aitesam961/Cattle-Health-Monitoring-WSN/Documentation/Video/CDC/20230429_175326.jpg

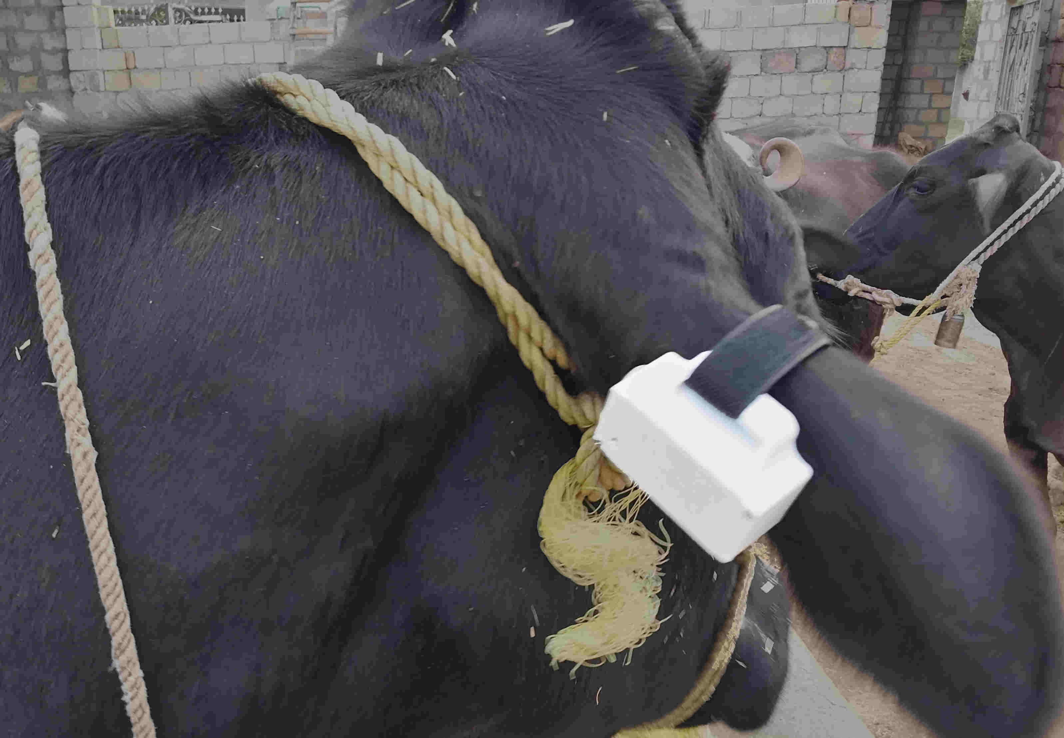
Documentation/Video/CDC/20230429_175326.jpg
