aitesam961/Cattle-Health-Monitoring-WSN/Documentation/Video/CDC/20230429_175645.jpg

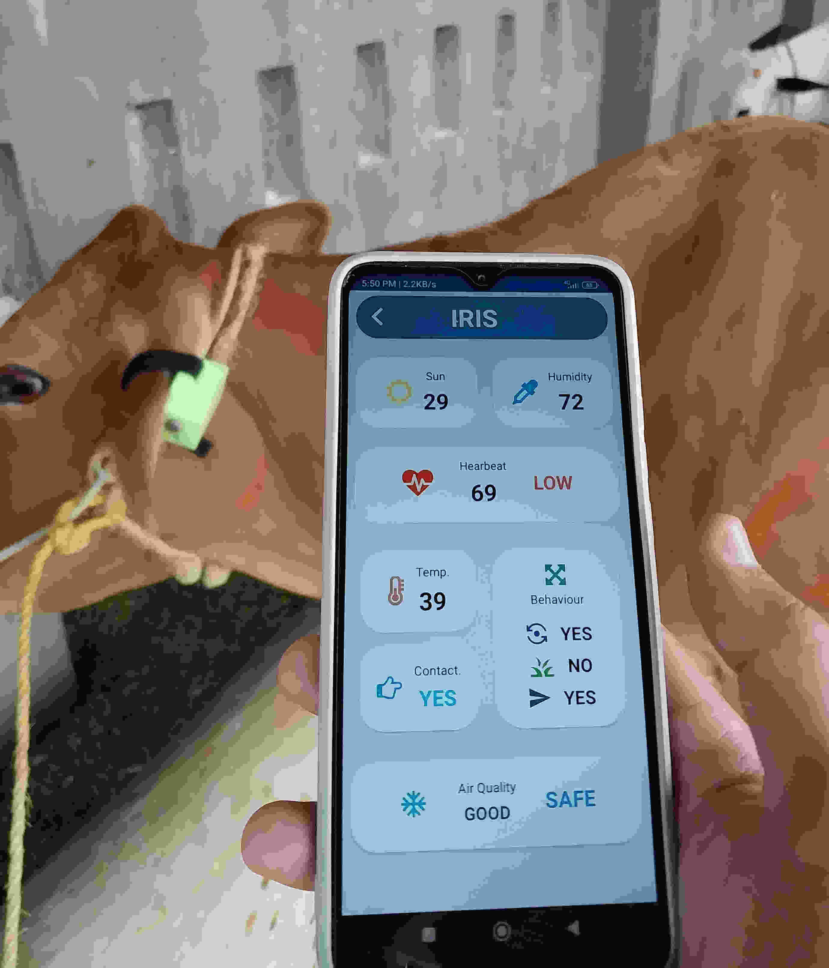
Documentation/Video/CDC/20230429_175645.jpg
