aitesam961/Cattle-Health-Monitoring-WSN/Documentation/Video/CDC/cows-7880154_1920_1_5.jpg

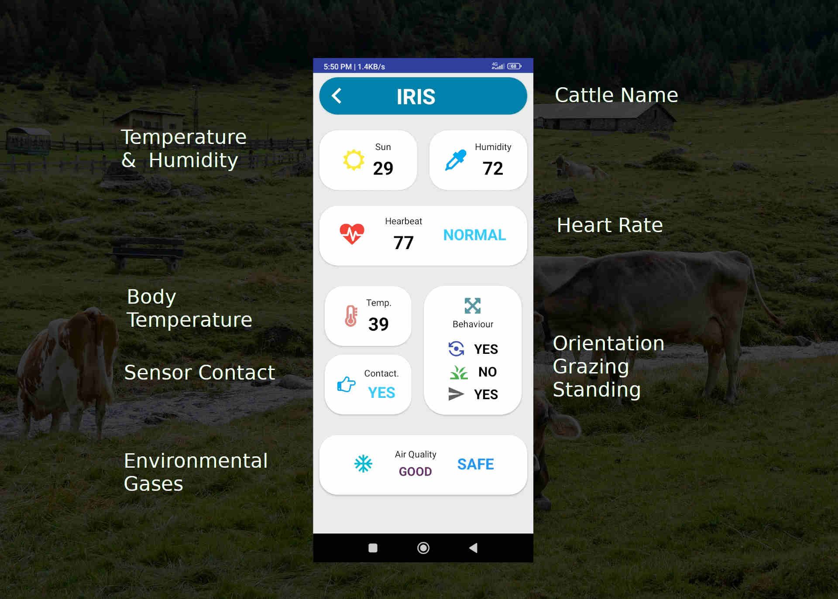
Documentation/Video/CDC/cows-7880154_1920_1_5.jpg
