aitesam961/Cattle-Health-Monitoring-WSN/Documentation/Video/CDC/IMG_20230511_132144.jpg

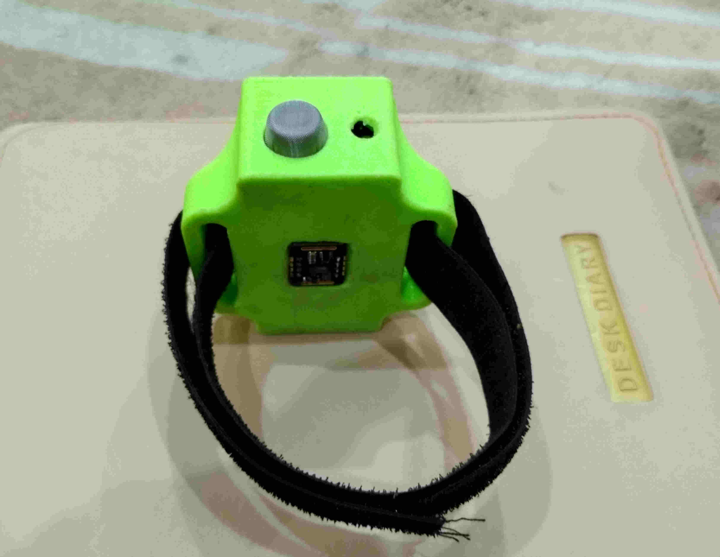
Documentation/Video/CDC/IMG_20230511_132144.jpg
