aitesam961/Cattle-Health-Monitoring-WSN/Documentation/Video/Video Workdir/cows-7990273_1920.jpg

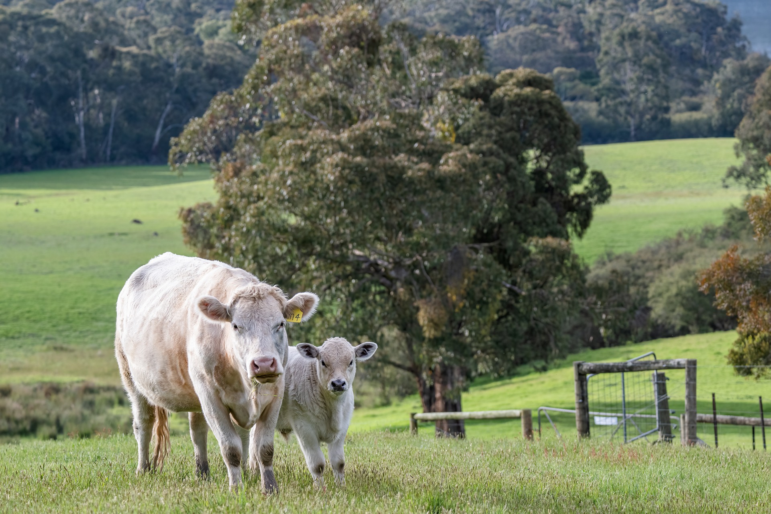
Documentation/Video/Video Workdir/cows-7990273_1920.jpg
