aitesam961/Cattle-Health-Monitoring-WSN/Documentation/Video/Video Workdir/DataAnalysis.jpg

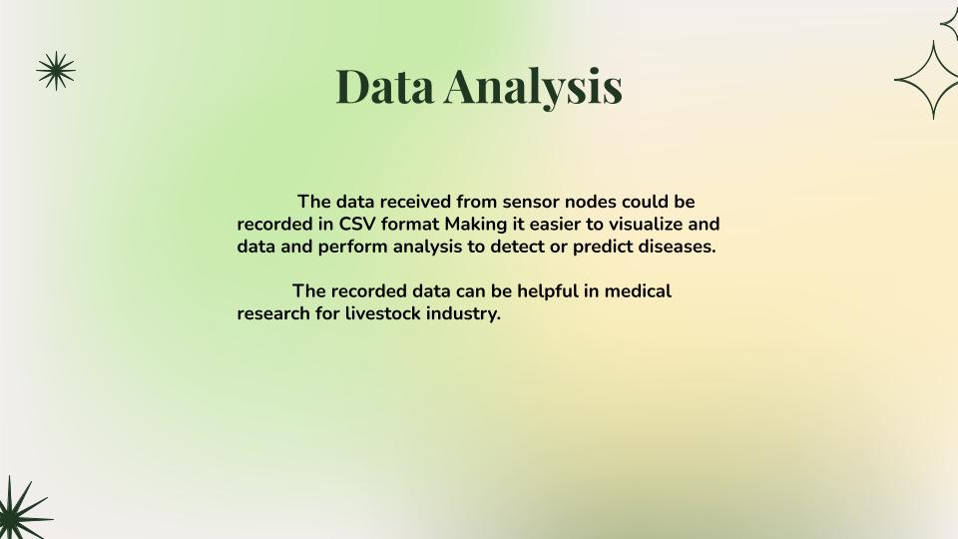
Documentation/Video/Video Workdir/DataAnalysis.jpg
