aitesam961/Cattle-Health-Monitoring-WSN/Documentation/Video/Video Workdir/farming-7290365_1920.jpg

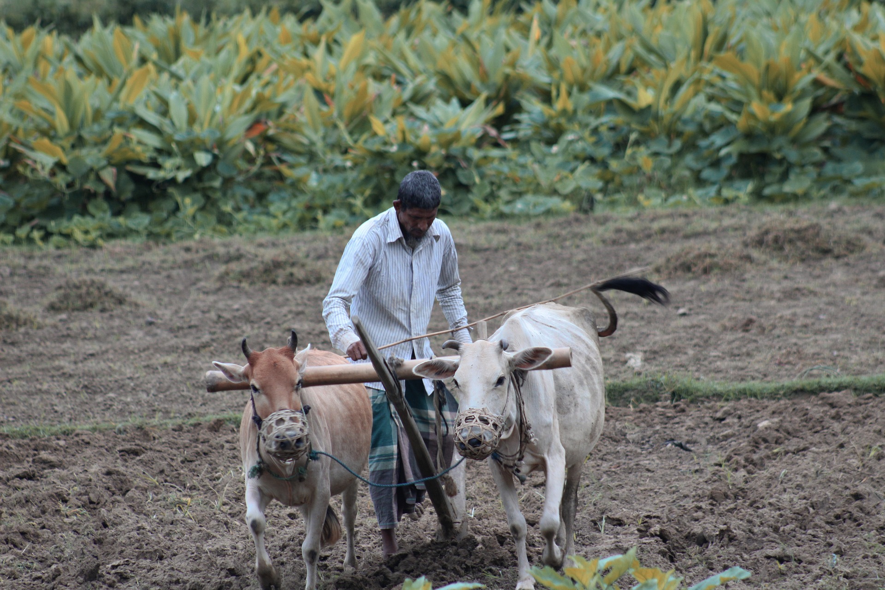
Documentation/Video/Video Workdir/farming-7290365_1920.jpg
