aitesam961/Cattle-Health-Monitoring-WSN/Documentation/Video/Video Workdir/fence-agriculture-cattle-livestock-farm-dairy-dairy-farming-crop-png-clipart.jpg

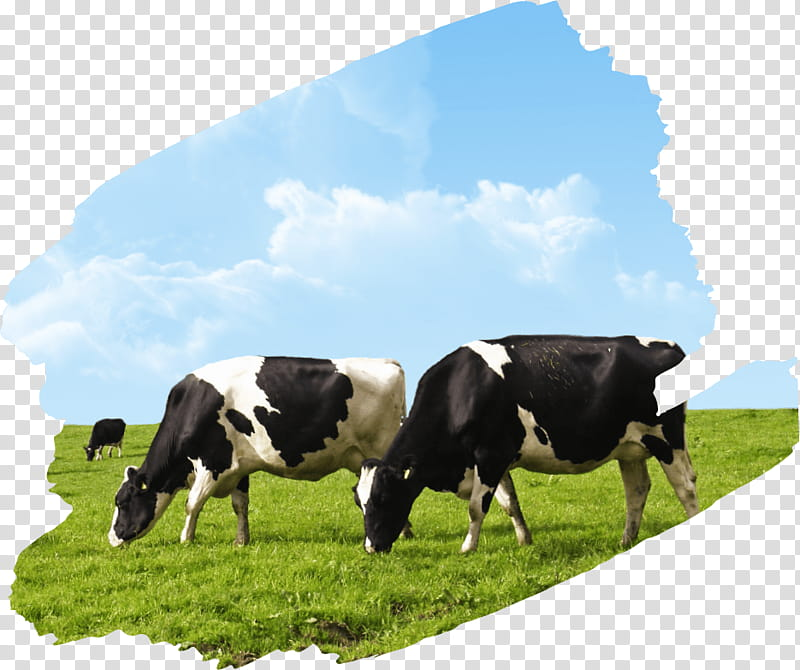
Documentation/Video/Video Workdir/fence-agriculture-cattle-livestock-farm-dairy-dairy-farming-crop-png-clipart.jpg
