aitesam961/Cattle-Health-Monitoring-WSN/Documentation/Video/Video Workdir/Health Status.jpg

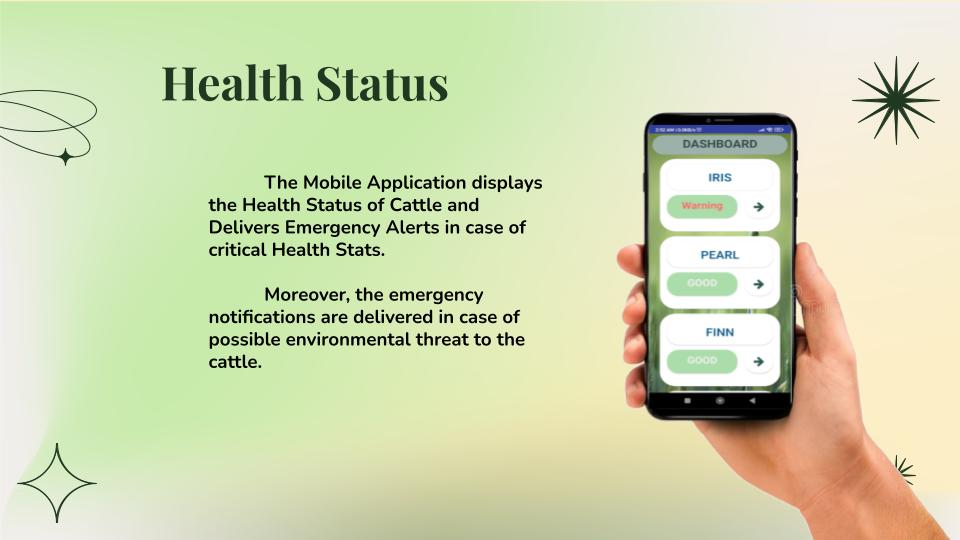
Documentation/Video/Video Workdir/Health Status.jpg
