aitesam961/Cattle-Health-Monitoring-WSN/Documentation/Video/Video Workdir/Intro.jpg

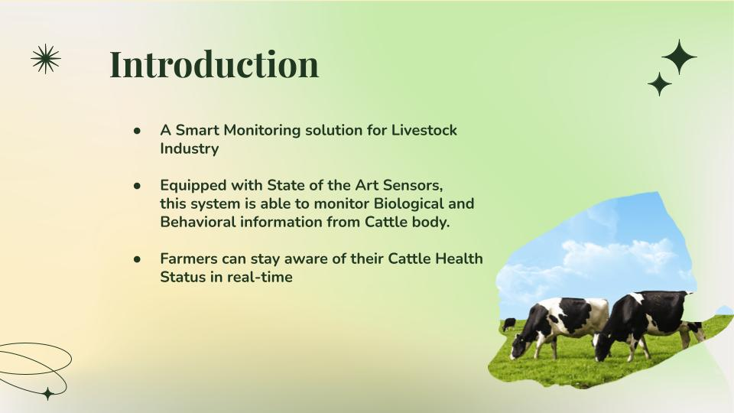
Documentation/Video/Video Workdir/Intro.jpg
