aitesam961/Cattle-Health-Monitoring-WSN/Documentation/Video/Video Workdir/Motivation.jpg

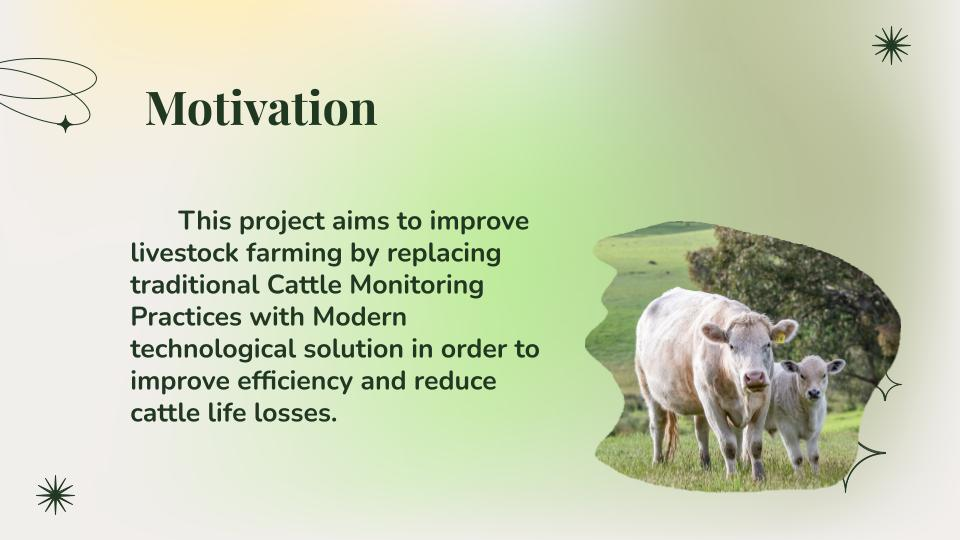
Documentation/Video/Video Workdir/Motivation.jpg
