aitesam961/Cattle-Health-Monitoring-WSN/Documentation/Video/Video Workdir/samsung_phone Frame.jpg

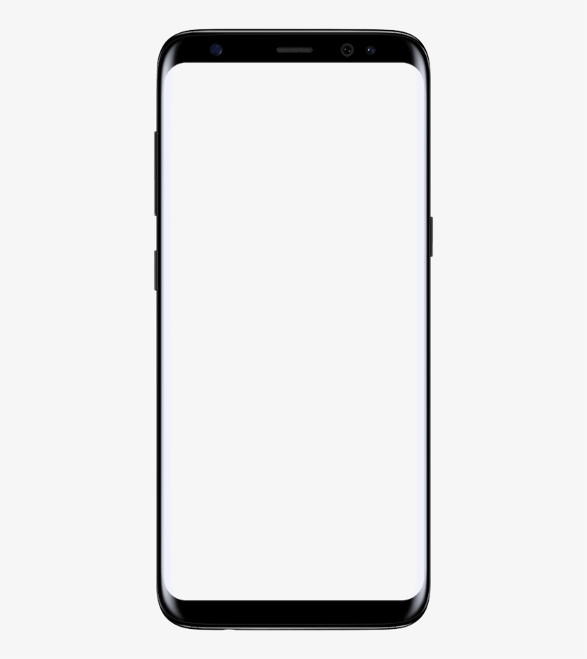
Documentation/Video/Video Workdir/samsung_phone Frame.jpg
