aitesam961/Cattle-Health-Monitoring-WSN/Documentation/Video/Video Workdir/Solution.jpg

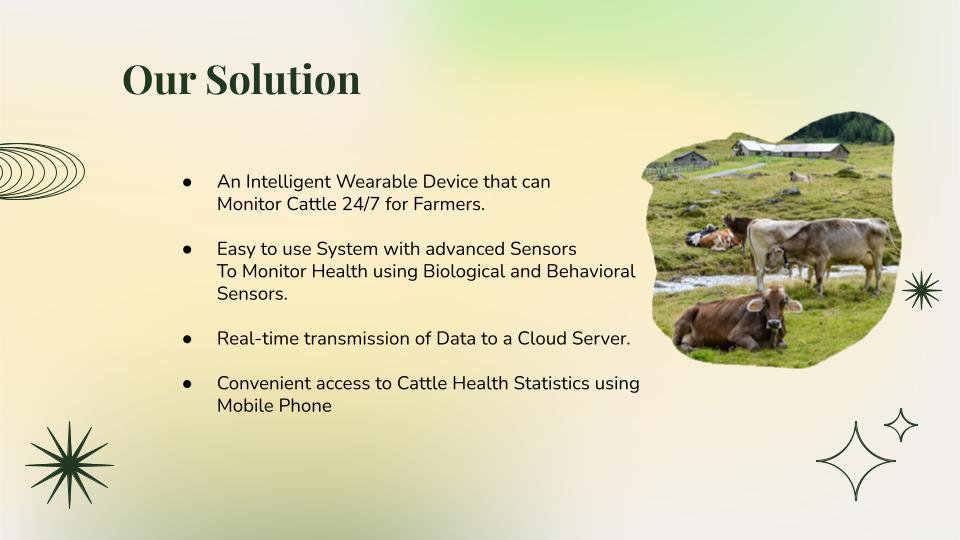
Documentation/Video/Video Workdir/Solution.jpg
