aitesam961/Cattle-Health-Monitoring-WSN/Documentation/Video/Video Workdir/Thanks.jpg

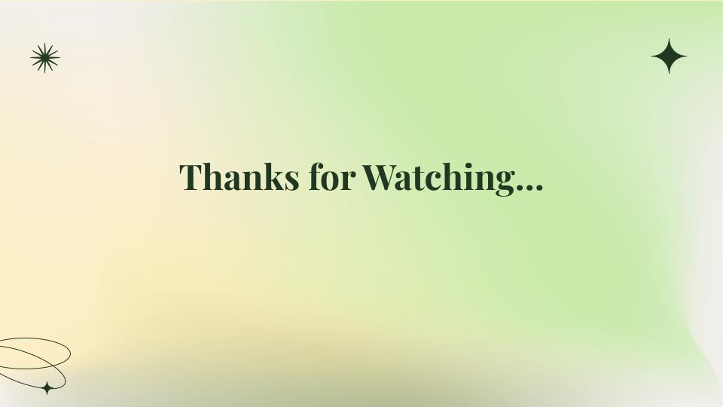
Documentation/Video/Video Workdir/Thanks.jpg
