aitesam961/Cattle-Health-Monitoring-WSN/Documentation/Video/Video Workdir/UserInterface.jpg

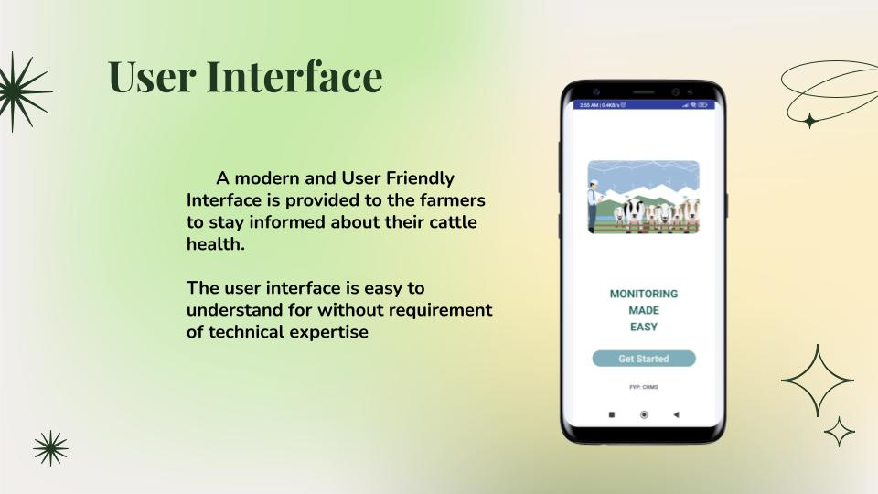
Documentation/Video/Video Workdir/UserInterface.jpg
