aitesam961/Cattle-Health-Monitoring-WSN/Documentation/Video/Video Workdir/Video Files/20230429_175326.jpg

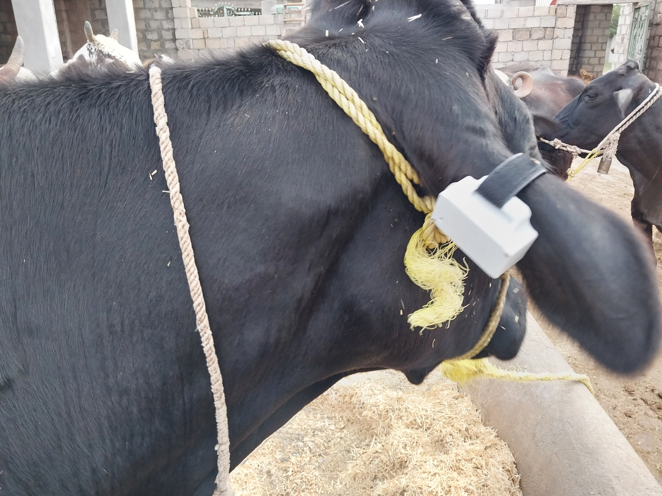
Documentation/Video/Video Workdir/Video Files/20230429_175326.jpg
