aitesam961/Cattle-Health-Monitoring-WSN/Documentation/Video/Video Workdir/Video Files/cows-7880154_1920.png

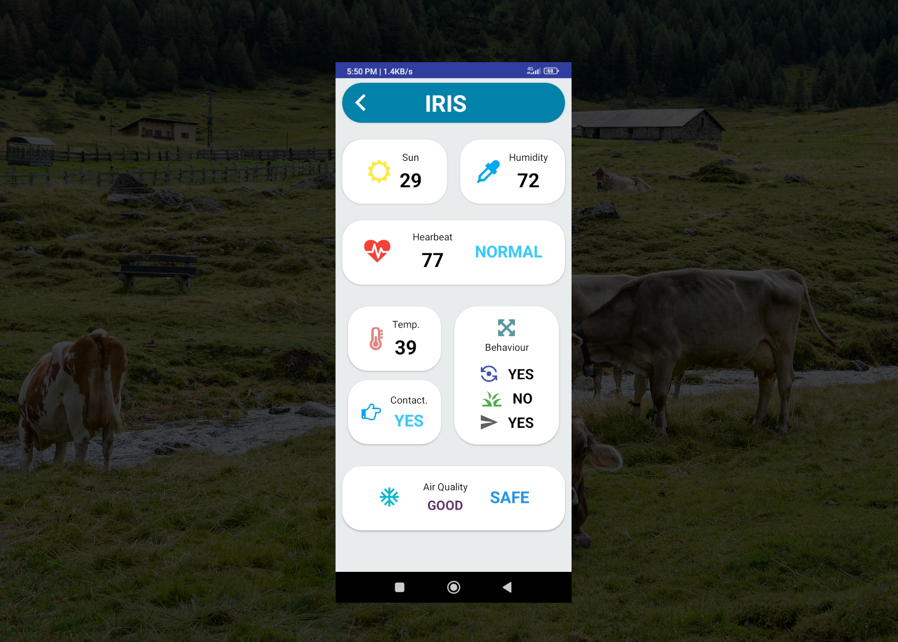
Documentation/Video/Video Workdir/Video Files/cows-7880154_1920.png
