aitesam961/Cattle-Health-Monitoring-WSN/Documentation/Video/Video Workdir/Video Files/drive-download-20230511T083015Z-001/IMG_20230511_132144.jpg

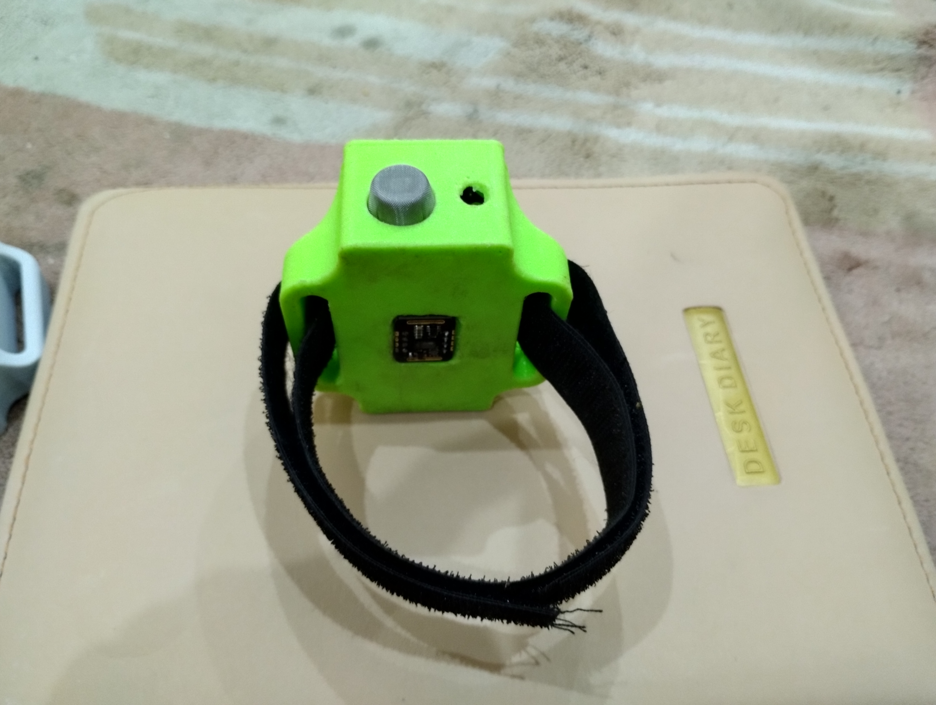
Documentation/Video/Video Workdir/Video Files/drive-download-20230511T083015Z-001/IMG_20230511_132144.jpg
