aitesam961/Cattle-Health-Monitoring-WSN/Documentation/Video/Video Workdir/Video Files/livestock-601277_1920.jpg

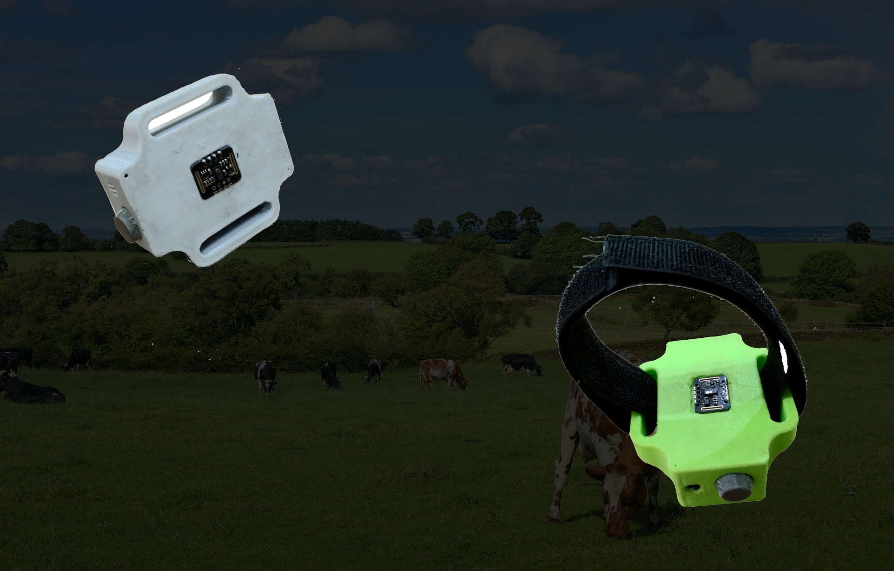
Documentation/Video/Video Workdir/Video Files/livestock-601277_1920.jpg
