aitesam961/Cattle-Health-Monitoring-WSN/Documentation/Video/Video Workdir/Video Files/Playlist/agriculture-7177221_1920.png

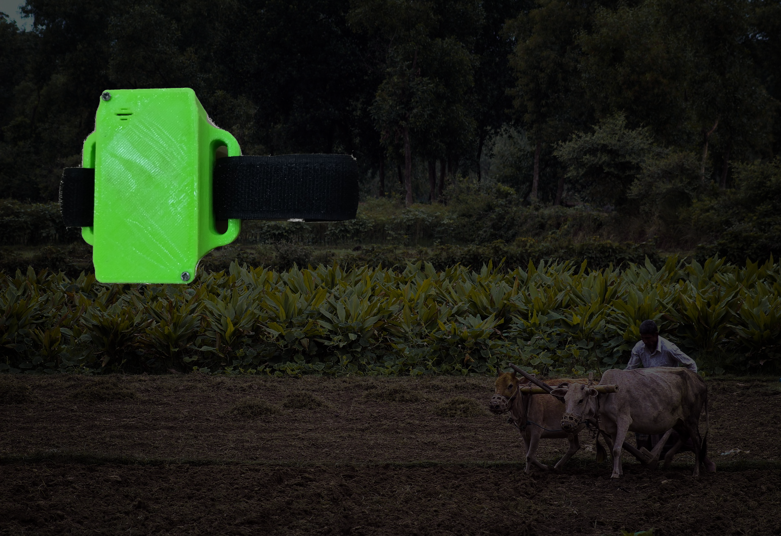
Documentation/Video/Video Workdir/Video Files/Playlist/agriculture-7177221_1920.png
