aitesam961/Cattle-Health-Monitoring-WSN/Documentation/Video/Video Workdir/Video Files/Screenshot_2023-04-29-17-49-31-431_com.firebase.iot.CHMS.jpg

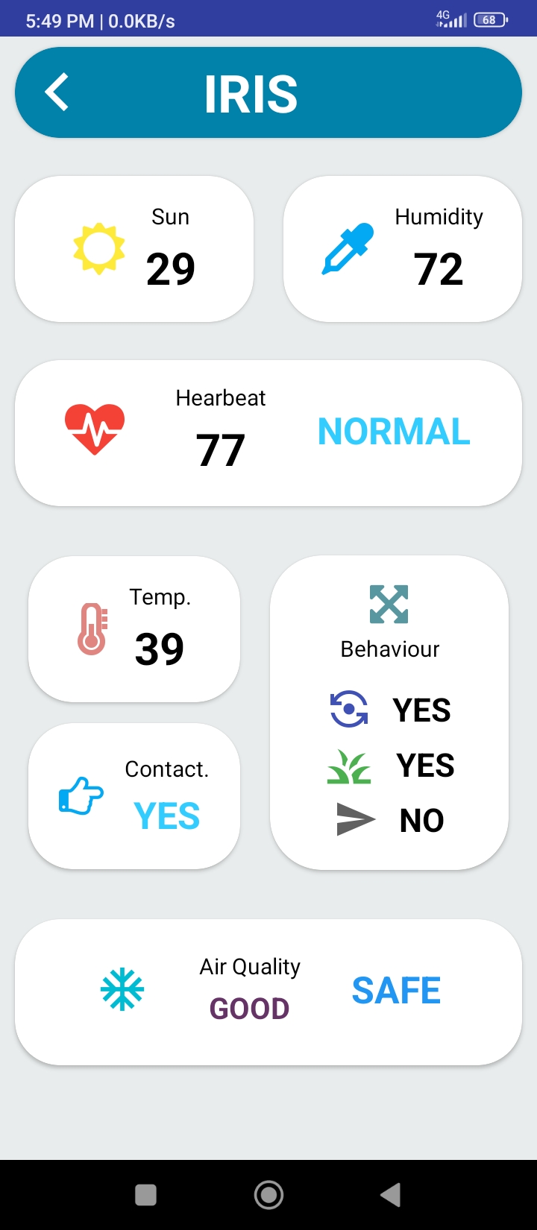
Documentation/Video/Video Workdir/Video Files/Screenshot_2023-04-29-17-49-31-431_com.firebase.iot.CHMS.jpg
