aitesam961/Cattle-Health-Monitoring-WSN/Documentation/Video/Video Workdir/Video Files/Temp-20230509T132613Z-001/livestock-601277_1920.jpg

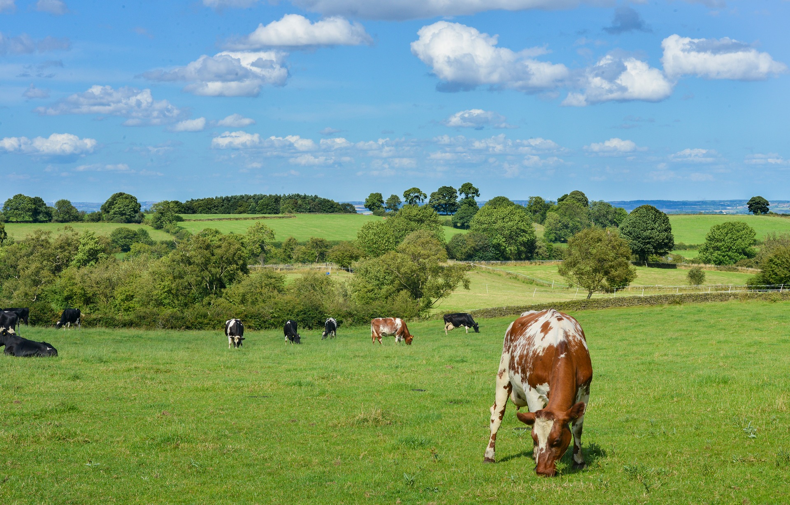
Documentation/Video/Video Workdir/Video Files/Temp-20230509T132613Z-001/livestock-601277_1920.jpg
