aitesam961/Cattle-Health-Monitoring-WSN/Documentation/Video/Video Workdir/Video Files/Temp-20230509T132613Z-001/Temp/1681420106222.jpg

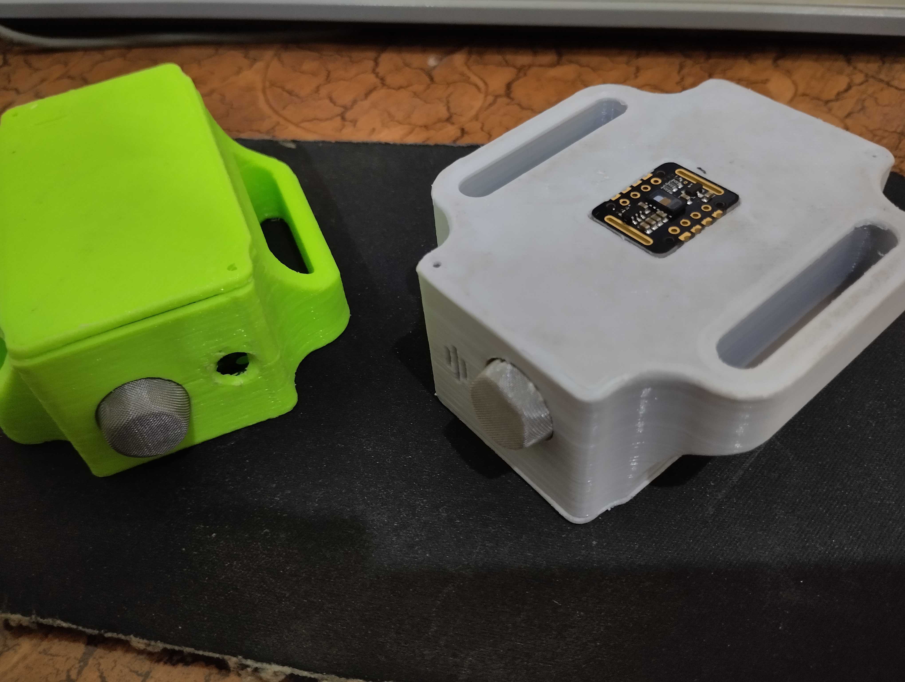
Documentation/Video/Video Workdir/Video Files/Temp-20230509T132613Z-001/Temp/1681420106222.jpg
