aitesam961/Cattle-Health-Monitoring-WSN/Documentation/Video/Video Workdir/Video Files/Temp-20230509T132613Z-001/Temp/Shortlisted/20230429_175330.jpg

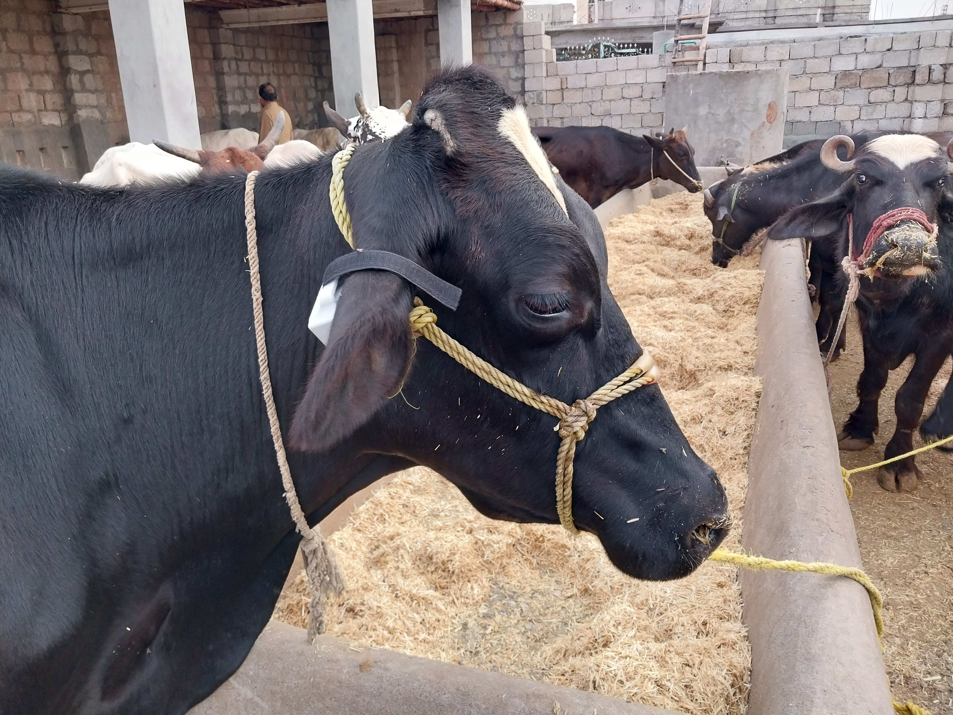
Documentation/Video/Video Workdir/Video Files/Temp-20230509T132613Z-001/Temp/Shortlisted/20230429_175330.jpg
