aitesam961/Cattle-Health-Monitoring-WSN/Documentation/Video/Video Workdir/Video Files/Temp-20230509T132613Z-001/Temp/Shortlisted/Screenshot_2023-04-29-17-50-25-605_com.firebase.iot.CHMS.jpg

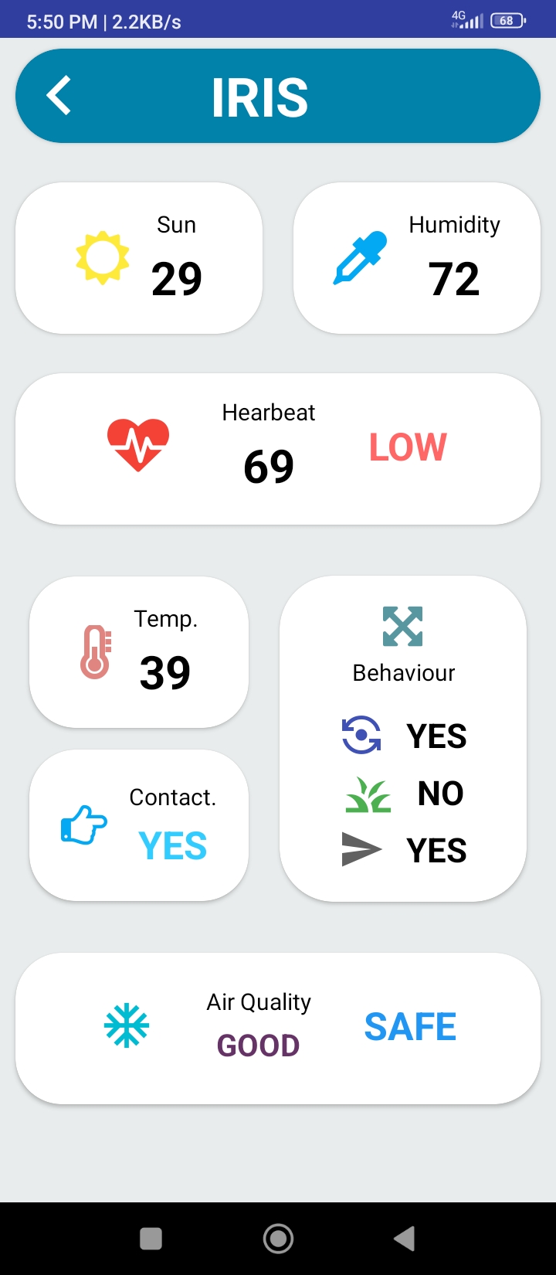
Documentation/Video/Video Workdir/Video Files/Temp-20230509T132613Z-001/Temp/Shortlisted/Screenshot_2023-04-29-17-50-25-605_com.firebase.iot.CHMS.jpg
