aitesam961/Cattle-Health-Monitoring-WSN/Documentation/Video/Video Workdir/WhatsApp Image 2023-05-23 at 2.52.53 AM.jpeg

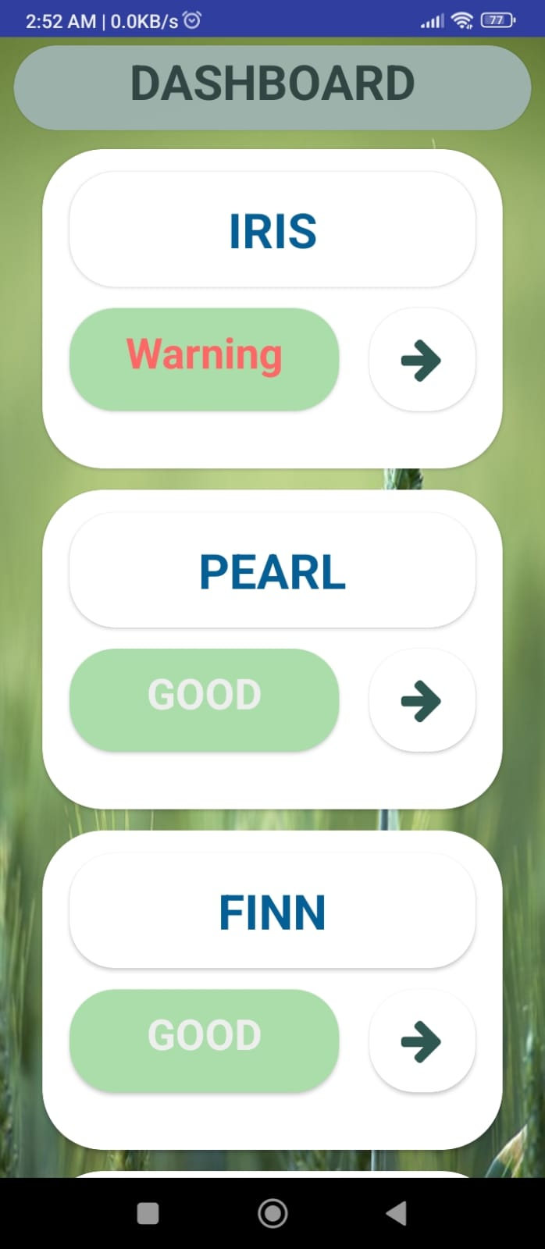
Documentation/Video/Video Workdir/WhatsApp Image 2023-05-23 at 2.52.53 AM.jpeg
