aitesam961/Cattle-Health-Monitoring-WSN/Documentation/Video/Video Workdir/Video Files/IRIS Data Capture - Sheet1.pdf

# IRIS Data Capture

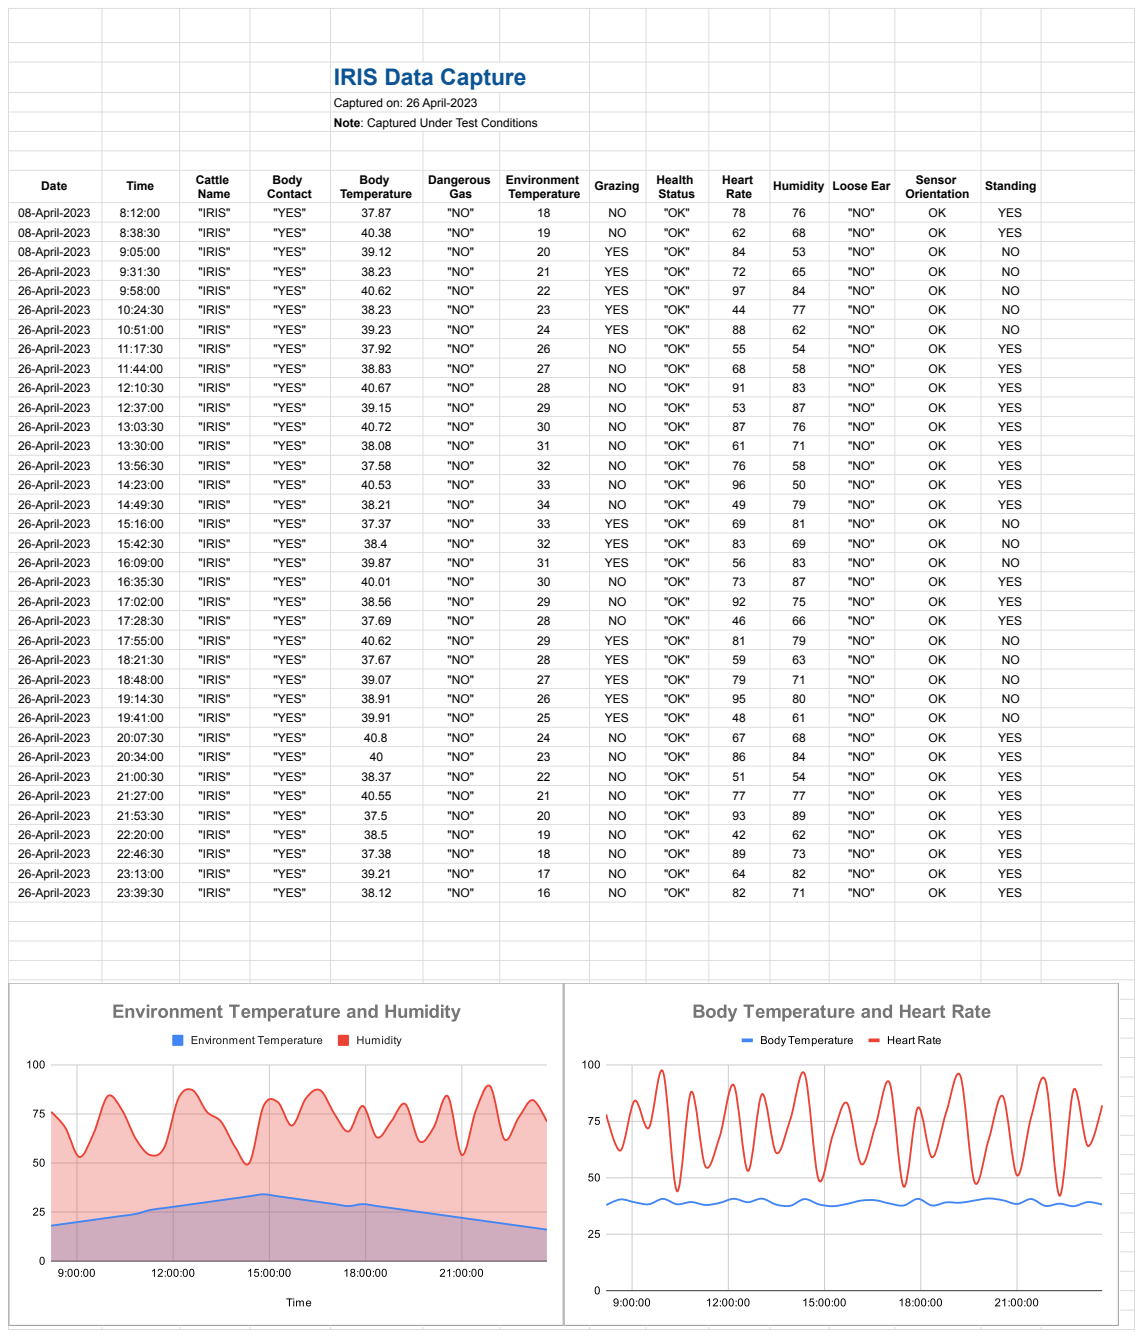
[picture p85: page 1]
Date; Time; Cattle Name; Body Contact; Body Temperature; Dangerous Gas; Environment; Temperature; Grazing; Health Status; Heart Rate; Humidity Loose Ear; Sensor Orientation; Standing; 08-April-2023; "IRIS"; "YES"; YES; 26-April-2023

Captured on: 26 April-2023
Note: Captured Under Test Conditions
