aitesam961/Cattle-Health-Monitoring-WSN/Arduino/ESP32-Firebase/Basic_test/Basic_test.ino

/**
 * Created by K. Suwatchai (Mobizt)
 *
 * Email: k_suwatchai@hotmail.com
 *
 * Github: https://github.com/mobizt/Firebase-ESP32
 *
 * Copyright (c) 2023 mobizt
 *
 */

#include <Arduino.h>
#if defined(ESP32)
#include <WiFi.h>
#include <FirebaseESP32.h>
#elif defined(ESP8266)
#include <ESP8266WiFi.h>
#include <FirebaseESP8266.h>
#elif defined(ARDUINO_RASPBERRY_PI_PICO_W)
#include <WiFi.h>
#include <FirebaseESP8266.h>
#endif

// Provide the token generation process info.
#include <addons/TokenHelper.h>

// Provide the RTDB payload printing info and other helper functions.
#include <addons/RTDBHelper.h>

/* 1. Define the WiFi credentials */
#define WIFI_SSID "WIFI_AP"
#define WIFI_PASSWORD "WIFI_PASSWORD"

// For the following credentials, see examples/Authentications/SignInAsUser/EmailPassword/EmailPassword.ino

/* 2. Define the API Key */
#define API_KEY "API_KEY"

/* 3. Define the RTDB URL */
#define DATABASE_URL "URL" //<databaseName>.firebaseio.com or <databaseName>.<region>.firebasedatabase.app

/* 4. Define the user Email and password that alreadey registerd or added in your project */
#define USER_EMAIL "USER_EMAIL"
#define USER_PASSWORD "USER_PASSWORD"

// Define Firebase Data object
FirebaseData fbdo;

FirebaseAuth auth;
FirebaseConfig config;

unsigned long sendDataPrevMillis = 0;

unsigned long count = 0;

void setup()
{

  Serial.begin(115200);

  WiFi.begin(WIFI_SSID, WIFI_PASSWORD);
  Serial.print("Connecting to Wi-Fi");
  while (WiFi.status() != WL_CONNECTED)
  {
    Serial.print(".");
    delay(300);
  }
  Serial.println();
  Serial.print("Connected with IP: ");
  Serial.println(WiFi.localIP());
  Serial.println();

  Serial.printf("Firebase Client v%s\n\n", FIREBASE_CLIENT_VERSION);

  /* Assign the api key (required) */
  config.api_key = API_KEY;

  /* Assign the user sign in credentials */
  auth.user.email = USER_EMAIL;
  auth.user.password = USER_PASSWORD;

  /* Assign the RTDB URL (required) */
  config.database_url = DATABASE_URL;

  /* Assign the callback function for the long running token generation task */
  config.token_status_callback = tokenStatusCallback; // see addons/TokenHelper.h

  // Or use legacy authenticate method
  // config.database_url = DATABASE_URL;
  // config.signer.tokens.legacy_token = "<database secret>";

  // To connect without auth in Test Mode, see Authentications/TestMode/TestMode.ino

  //////////////////////////////////////////////////////////////////////////////////////////////
  // Please make sure the device free Heap is not lower than 80 k for ESP32 and 10 k for ESP8266,
  // otherwise the SSL connection will fail.
  //////////////////////////////////////////////////////////////////////////////////////////////

  Firebase.begin(&config, &auth);

  // Comment or pass false value when WiFi reconnection will control by your code or third party library
  Firebase.reconnectWiFi(true);

  Firebase.setDoubleDigits(5);

  /** Timeout options.

  //WiFi reconnect timeout (interval) in ms (10 sec - 5 min) when WiFi disconnected.
  config.timeout.wifiReconnect = 10 * 1000;

  //Socket connection and SSL handshake timeout in ms (1 sec - 1 min).
  config.timeout.socketConnection = 10 * 1000;

  //Server response read timeout in ms (1 sec - 1 min).
  config.timeout.serverResponse = 10 * 1000;

  //RTDB Stream keep-alive timeout in ms (20 sec - 2 min) when no server's keep-alive event data received.
  config.timeout.rtdbKeepAlive = 45 * 1000;

  //RTDB Stream reconnect timeout (interval) in ms (1 sec - 1 min) when RTDB Stream closed and want to resume.
  config.timeout.rtdbStreamReconnect = 1 * 1000;

  //RTDB Stream error notification timeout (interval) in ms (3 sec - 30 sec). It determines how often the readStream
  //will return false (error) when it called repeatedly in loop.
  config.timeout.rtdbStreamError = 3 * 1000;

  Note:
  The function that starting the new TCP session i.e. first time server connection or previous session was closed, the function won't exit until the
  time of config.timeout.socketConnection.

  You can also set the TCP data sending retry with
  config.tcp_data_sending_retry = 1;

  */
}

void loop()
{

  // Firebase.ready() should be called repeatedly to handle authentication tasks.

  if (Firebase.ready() && (millis() - sendDataPrevMillis > 15000 || sendDataPrevMillis == 0))
  {
    sendDataPrevMillis = millis();

    Serial.printf("Set bool... %s\n", Firebase.setBool(fbdo, F("/test/bool"), count % 2 == 0) ? "ok" : fbdo.errorReason().c_str());

    Serial.printf("Get bool... %s\n", Firebase.getBool(fbdo, FPSTR("/test/bool")) ? fbdo.to<bool>() ? "true" : "false" : fbdo.errorReason().c_str());

    bool bVal;
    Serial.printf("Get bool ref... %s\n", Firebase.getBool(fbdo, F("/test/bool"), &bVal) ? bVal ? "true" : "false" : fbdo.errorReason().c_str());

    Serial.printf("Set int... %s\n", Firebase.setInt(fbdo, F("/test/int"), count) ? "ok" : fbdo.errorReason().c_str());

    Serial.printf("Get int... %s\n", Firebase.getInt(fbdo, F("/test/int")) ? String(fbdo.to<int>()).c_str() : fbdo.errorReason().c_str());

    int iVal = 0;
    Serial.printf("Get int ref... %s\n", Firebase.getInt(fbdo, F("/test/int"), &iVal) ? String(iVal).c_str() : fbdo.errorReason().c_str());

    Serial.printf("Set float... %s\n", Firebase.setFloat(fbdo, F("/test/float"), count + 10.2) ? "ok" : fbdo.errorReason().c_str());

    Serial.printf("Get float... %s\n", Firebase.getFloat(fbdo, F("/test/float")) ? String(fbdo.to<float>()).c_str() : fbdo.errorReason().c_str());

    Serial.printf("Set double... %s\n", Firebase.setDouble(fbdo, F("/test/double"), count + 35.517549723765) ? "ok" : fbdo.errorReason().c_str());

    Serial.printf("Get double... %s\n", Firebase.getDouble(fbdo, F("/test/double")) ? String(fbdo.to<double>()).c_str() : fbdo.errorReason().c_str());

    Serial.printf("Set string... %s\n", Firebase.setString(fbdo, F("/test/string"), "Hello World!") ? "ok" : fbdo.errorReason().c_str());

    Serial.printf("Get string... %s\n", Firebase.getString(fbdo, F("/test/string")) ? fbdo.to<const char *>() : fbdo.errorReason().c_str());

    // For the usage of FirebaseJson, see examples/FirebaseJson/BasicUsage/Create_Edit_Parse.ino
    FirebaseJson json;

    if (count == 0)
    {
      json.set("value/round/" + String(count), F("cool!"));
      json.set(F("vaue/ts/.sv"), F("timestamp"));
      Serial.printf("Set json... %s\n", Firebase.set(fbdo, F("/test/json"), json) ? "ok" : fbdo.errorReason().c_str());
    }
    else
    {
      json.add(String(count), "smart!");
      Serial.printf("Update node... %s\n", Firebase.updateNode(fbdo, F("/test/json/value/round"), json) ? "ok" : fbdo.errorReason().c_str());
    }

    Serial.println();

    // For generic set/get functions.

    // For generic set, use Firebase.set(fbdo, <path>, <any variable or value>)

    // For generic get, use Firebase.get(fbdo, <path>).
    // And check its type with fbdo.dataType() or fbdo.dataTypeEnum() and
    // cast the value from it e.g. fbdo.to<int>(), fbdo.to<std::string>().

    // The function, fbdo.dataType() returns types String e.g. string, boolean,
    // int, float, double, json, array, blob, file and null.

    // The function, fbdo.dataTypeEnum() returns type enum (number) e.g. fb_esp_rtdb_data_type_null (1),
    // fb_esp_rtdb_data_type_integer, fb_esp_rtdb_data_type_float, fb_esp_rtdb_data_type_double,
    // fb_esp_rtdb_data_type_boolean, fb_esp_rtdb_data_type_string, fb_esp_rtdb_data_type_json,
    // fb_esp_rtdb_data_type_array, fb_esp_rtdb_data_type_blob, and fb_esp_rtdb_data_type_file (10)

    count++;
  }
}

/// PLEASE AVOID THIS ////

// Please avoid the following inappropriate and inefficient use cases
/**
 *
 * 1. Call get repeatedly inside the loop without the appropriate timing for execution provided e.g. millis() or conditional checking,
 * where delay should be avoided.
 *
 * Everytime get was called, the request header need to be sent to server which its size depends on the authentication method used,
 * and costs your data usage.
 *
 * Please use stream function instead for this use case.
 *
 * 2. Using the single FirebaseData object to call different type functions as above example without the appropriate
 * timing for execution provided in the loop i.e., repeatedly switching call between get and set functions.
 *
 * In addition to costs the data usage, the delay will be involved as the session needs to be closed and opened too often
 * due to the HTTP method (GET, PUT, POST, PATCH and DELETE) was changed in the incoming request.
 *
 *
 * Please reduce the use of swithing calls by store the multiple values to the JSON object and store it once on the database.
 *
 * Or calling continuously "set" or "setAsync" functions without "get" called in between, and calling get continuously without set
 * called in between.
 *
 * If you needed to call arbitrary "get" and "set" based on condition or event, use another FirebaseData object to avoid the session
 * closing and reopening.
 *
 * 3. Use of delay or hidden delay or blocking operation to wait for hardware ready in the third party sensor libraries, together with stream functions e.g. Firebase.RTDB.readStream and fbdo.streamAvailable in the loop.
 *
 * Please use non-blocking mode of sensor libraries (if available) or use millis instead of delay in your code.
 *
 * 4. Blocking the token generation process.
 *
 * Let the authentication token generation to run without blocking, the following code MUST BE AVOIDED.
 *
 * while (!Firebase.ready()) <---- Don't do this in while loop
 * {
 *     delay(1000);
 * }
 *
 */
