aitesam961/Cattle-Health-Monitoring-WSN/Arduino/Basic_test/accel/accel.ino

#include <Arduino.h>
#include <Wire.h>
#include <MPU6050.h>

MPU6050 mpu;

void setup() {
  Serial.begin(115200);
  Wire.begin();
  mpu.initialize();
  mpu.setFullScaleAccelRange(MPU6050_ACCEL_FS_2);
}

void loop() {
  int16_t ax, ay, az;
  mpu.getAcceleration(&ax, &ay, &az);
  Serial.print("X acceleration: ");
  Serial.println(ax);
  delay(500);
}
