aitesam961/Cattle-Health-Monitoring-WSN/Arduino/Basic_test/accel/motion_detection/motion_detection.ino

#include <Adafruit_MPU6050.h>
#include <Adafruit_Sensor.h>
#include <Wire.h>

Adafruit_MPU6050 mpu;

void setup(void) {
  Serial.begin(115200);
  while (!Serial)
    delay(10); // will pause Zero, Leonardo, etc until serial console opens

  Serial.println("Adafruit MPU6050 test!");

  // Try to initialize!
  if (!mpu.begin()) {
    Serial.println("Failed to find MPU6050 chip");
    while (1) {
      delay(10);
    }
  }
  Serial.println("MPU6050 Found!");

  mpu.setHighPassFilter(MPU6050_HIGHPASS_0_63_HZ);
  mpu.setMotionDetectionThreshold(1);
  mpu.setMotionDetectionDuration(20);
  mpu.setInterruptPinLatch(true);	// Keep it latched.  Will turn off when reinitialized.
  mpu.setInterruptPinPolarity(true);
  mpu.setMotionInterrupt(true);

  Serial.println("");
  delay(100);
}

void loop() {

  if(mpu.getMotionInterruptStatus()) {
    /* Get new sensor events with the readings */
    sensors_event_t a, g, temp;
    mpu.getEvent(&a, &g, &temp);

    /* Print out the values */
    Serial.print("AccelX:");
    Serial.print(a.acceleration.x);
    Serial.print(",");
    Serial.print("AccelY:");
    Serial.print(a.acceleration.y);
    Serial.print(",");
    Serial.print("AccelZ:");
    Serial.print(a.acceleration.z);
    Serial.print(", ");
    Serial.print("GyroX:");
    Serial.print(g.gyro.x);
    Serial.print(",");
    Serial.print("GyroY:");
    Serial.print(g.gyro.y);
    Serial.print(",");
    Serial.print("GyroZ:");
    Serial.print(g.gyro.z);
    Serial.print ("     ,");
    
    
    if(a.acceleration.z>5 and  a.acceleration.x >-4 or a.acceleration.x > 5 ){
    Serial.println("Sensor Position: WRONG");
    
    }
    else
    {
        Serial.print("Sensor Position: OK");
        Serial.print(",   ");
        if(a.acceleration.x <-5 &&  a.acceleration.z <-5){
          Serial.print("Grazing");
        }
        else if(a.acceleration.x <5 &&  a.acceleration.z >-5){
          Serial.print("Standing");
        }
        else if(a.acceleration.x >-5 &&  a.acceleration.y >5)
        {
          Serial.print("Loose Ear");
        }
        Serial.println("  ");
   }
   
  }
  delay(10);
}
