aitesam961/Cattle-Health-Monitoring-WSN/Blink-test/Blink-test.ino

// the setup function runs once when you press reset or power the board
void setup() {
  Serial.begin(115200);
  Serial.print("System Booting");
  
  // initialize digital pin LED_BUILTIN as an output.
  pinMode(2, OUTPUT);
}

// the loop function runs over and over again forever
void loop() {
  Serial.print("ON");
  digitalWrite(2, HIGH);   // turn the LED on (HIGH is the voltage level)
  delay(1000);   
  Serial.print("OFF");// wait for a second
  digitalWrite(2, LOW);    // turn the LED off by making the voltage LOW
  delay(1000);                       // wait for a second
}
