aitesam961/Cattle-Health-Monitoring-WSN/Test-Branch/ESP32-WiFi-Check/src/main.cpp

#include <Arduino.h>
#include <WiFi.h>
void setup() {
  Serial.begin(115200);
  WiFi.begin("aitesam961", "aitesam961");
  // Wait for wifi to be connected
  uint32_t notConnectedCounter = 0;
  while (WiFi.status() != WL_CONNECTED) {
      delay(100);
      Serial.println("Wifi connecting...");
      notConnectedCounter++;
      if(notConnectedCounter > 150) { // Reset board if not connected after 5s
          Serial.println("Resetting due to Wifi not connecting...");
          ESP.restart();
      }
  }
  Serial.print("Wifi connected, IP address: ");
  Serial.println(WiFi.localIP());
}
void loop() {
  // put your main code here, to run repeatedly:
}
